Seitanas/abp/src/config.h

#define PASSWORD "1111"
#define RECIPIENT "+11133333"
#define BUZZER 0
#define ARMED_LED 1
#define DOOR 2
#define WINDOW 3
#define POWER 5
#define ARM_BUTTON 6
#define SIREN 4
#define ARMING_SECONDS 10
#define SENSOR1 "/sys/bus/w1/devices/28-0000061f19fb/w1_slave"
#define SENSOR2 "/sys/bus/w1/devices/28-00000620589f/w1_slave"
